dmpop/tomodachi/Documentation/_res/bookcover/bookcover.png

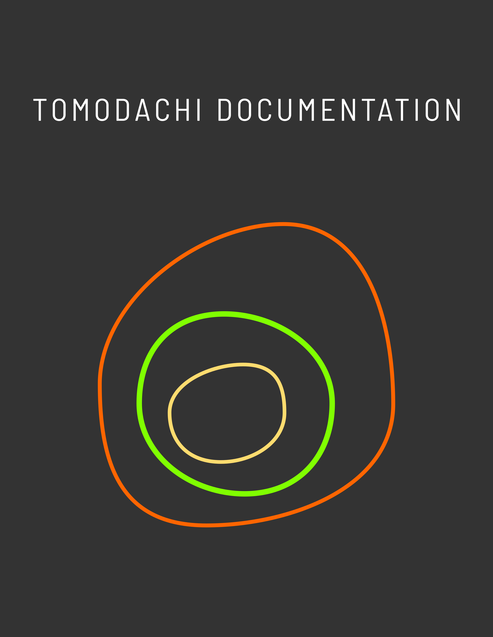
Documentation/_res/bookcover/bookcover.png
